michaelbolt/ElectronicBusinessCard/game.h

/*
 * game.h
 *
 * Created on: May 13, 2020
 *     Author: Michael Bolt
 */

#ifndef GAME_H_
#define GAME_H_

#include <stdint.h>
#include "hardware.h"
#include "ssd1306.h"


/********************
 * Player Character *
 ********************/
// constant defines
#define PLAYER_X_POSITION       2       // x position of sprite
#define PLAYER_Y_MAX            19      // max y position
#define PLAYER_SPEED_MAX        3       // max y speed
#define PLAYER_SPEED_STEP       1       // y speed step
#define PLAYER_STATE_NORMAL     0x01    // normal state
#define PLAYER_STATE_EXPLODED   0x00    // exploded state
#define PLAYER_LASER_DELAY      4       // number of frames between consecutive lasers
#define PLAYER_RESPAWN_DELAY    32      // number of frames between player death and respawn
extern const uint8_t playerShip[][8];   // player sprite defined in gameSprites.h
// struct definition
typedef struct PLAYER_S {
    // physics
    int16_t  y;             // y position
    int16_t  speed;         // y speed
    // flags/game logic
    uint16_t state;         // current player state
    uint16_t laserCounter;  // number of frames until next laser fire
    uint16_t keyFrame;      // which sprite keyFrame to draw
} Player;
// functions
void playerController(void);
void drawPlayer(void);

/**********
 * Lasers *
 **********/
// constant defines
#define LASER_SPEED             6       // x speed of lasers
#define LASER_STATE_ENABLED     1       // enabled state
#define LASER_STATE_DISABLED    0       // disabled state
#define LASER_TYPE_PLAYER       1       // use to fire player laser
#define LASER_TYPE_ENEMY        0       // use to fire enemy laser
#define LASER_MAX_PLAYER        3       // max number of player lasers
#define LASER_MAX_ENEMY         5       // max number of enemy lasers
// sprites defined in gameSprites.c
extern const uint8_t playerLaser[4][8];
extern const uint8_t acePilotLaser[4][8];
// struct definition
typedef struct LASER_S {
    // location
    int16_t x;          // x position
    int16_t y;          // y position
    // flags/game logic
    uint16_t enabled;   // current laser state
    uint16_t keyFrame;  // which sprite keyFrame to draw
} Laser;
// functions
void fireLaser(uint16_t type, uint16_t x, uint16_t y);
void updateLasers(void);
void drawLasers(void);

/********************
 * Enemy Characters *
 ********************/
// constant defines
#define MAX_ENEMIES             5   // maximum number of enemies onscreen
#define ENEMY_X_START           127 // starting x coordinate of enemies
#define ENEMY_Y_MAX             19  // max y position of enemies
#define ENEMY_SPAWN_RATE_MIN    8   // minimum frames between enemy spawn
#define ENEMY_TYPE_DISABLED     0   // inactive
#define ENEMY_TYPE_TORPEDO      1   // Interstellar Torpedo enemy
#define ENEMY_TYPE_BUZZ         2   // Buzz Drone enemy
#define ENEMY_TYPE_PILOT        3   // Ace Pilot enemy
#define ENEMY_TORPEDO_SPEED_0   5   // torpedo: initial speed
#define ENEMY_TORPEDO_DIVIDER   2   // torpedo: number of frames before speed increases (power of 2)
#define ENEMY_BUZZ_SPEED_X      2   // buzz: x speed magnitude
#define ENEMY_BUZZ_SPEED_Y      1   // buzz: y speed magnitude
#define ENEMY_BUZZ_UP           1   // buzz: moving upwards
#define ENEMY_BUZZ_DOWN         0   // buzz: moving downwards
#define ENEMY_PILOT_SPEED_X     2   // pilot: x speed magnitude
#define ENEMY_PILOT_SPEED_Y_MAX 2   // pilot: y speed max magnitude
#define ENEMY_PILOT_WINDOW      1
#define ENEMY_PILOT_LASER_COUNT 16  // pilot: number of frames betwen laser shots
// enemy sprites defined in gameSprites.c
extern const uint8_t interstellarTorpedo[4][8];
extern const uint8_t buzzDrone[4][8];
extern const uint8_t acePilot[4][8];
// struct definition
typedef struct ENEMY_S {
    // location
    int16_t x;          // x position
    int16_t y;          // y position
    // flags / game logic
    uint16_t type;      // current enemy state/type
    uint16_t keyFrame;  // which sprite keyFrame to draw
    int16_t  local;     // enemy-specific local variable
} Enemy;
// functions
void addEnemy(uint16_t type, uint16_t y);
void updateEnemies();
void drawEnemies();


/***********************
 * Collision Detection *
 ***********************/
// constants / defines
#define MAX_EXPLOSIONS              5
#define EXPLOSION_ANIMATION_LENGTH  8
#define EXPLOSION_STATE_ENABLED     1
#define EXPLOSION_STATE_DISABLED    0
extern const uint8_t explosion[8][8];
// struct definition re-using Laser
typedef Laser Explosion;
// functions
void addExplosion(uint16_t x, uint16_t y);
void checkCollisions();
void drawExplosions();


/**************
 * Game Logic *
 **************/
// constants / defines
#define DIGIT_WIDTH     4
extern const uint8_t digits[10][8];
#define LIFE_WIDTH      6
extern const uint8_t playerLife[1][8];
#define NEW_GAME        0
#define RESPAWN         1
#define HIGH_SCORE      0
#define PLAYER_SCORE    1
#define HIGH_SCORE_ANIMATION_LENGTH     (5*16)
#define RANDOM_NUMBER_SEED              0xB017
// functions
void gameInit(uint8_t respawn);
void drawScore(uint16_t score, uint16_t x, uint16_t y);
uint16_t drawLives(void);
uint16_t saveHighScore(void);
void highScoreAnimation(uint16_t animation_frame);
uint16_t randomNumber();

#endif  /* GAME_H_ */
